zhiyb/Nosumor/device/system/systick.h

#ifndef SYSTICK_H
#define SYSTICK_H

#include <stdint.h>
#include <list.h>

#ifdef __cplusplus
extern "C" {
#endif

typedef void (*const systick_handler_t)(uint32_t cnt);

void systick_init(uint32_t hz);
uint32_t systick_cnt();
void systick_delay(uint32_t cycles);

// Register a systick handler
#define SYSTICK_HANDLER(func)	LIST_ITEM(systick, systick_handler_t) = func

#ifdef __cplusplus
}
#endif

#endif // SYSTICK_H
